kagouraki/windSensorYachta/Pictures/Yachta_Details/IMG_20210728_142634032_HDR_kl.jpg

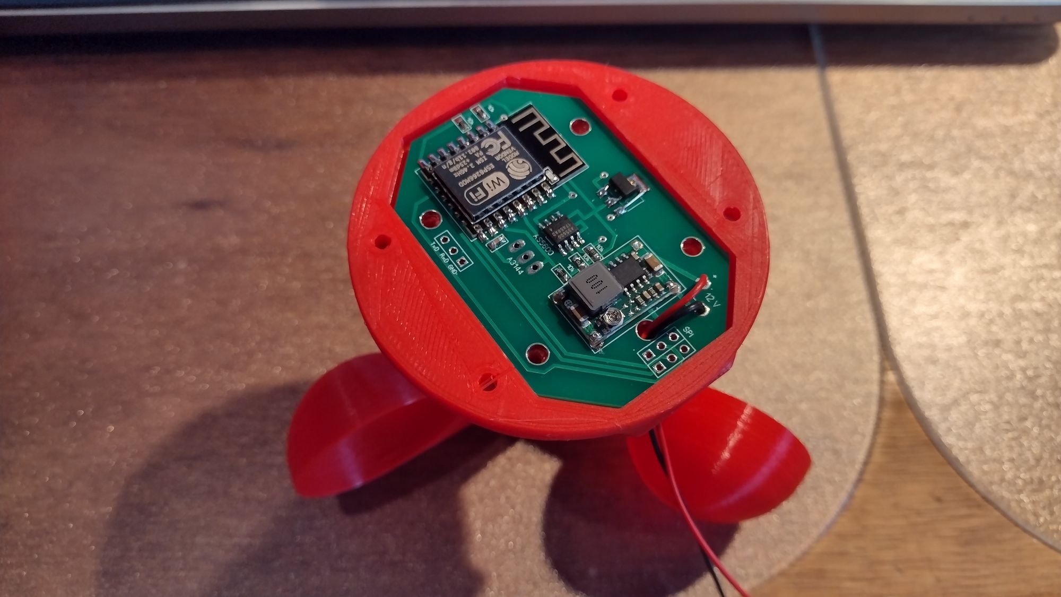
Pictures/Yachta_Details/IMG_20210728_142634032_HDR_kl.jpg
