kagouraki/windSensorYachta/Pictures/Yachta_Details/IMG_20210728_142640700_HDR_kl.jpg

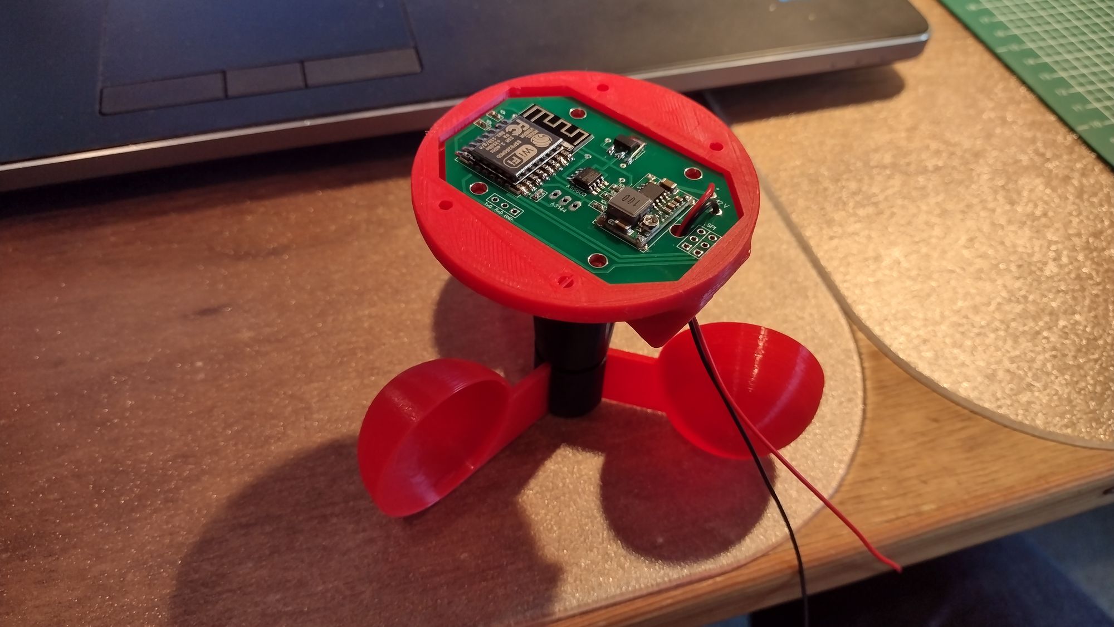
Pictures/Yachta_Details/IMG_20210728_142640700_HDR_kl.jpg
