kagouraki/windSensorYachta/Pictures/Yachta_Details/IMG_20210728_142648449_HDR_kl.jpg

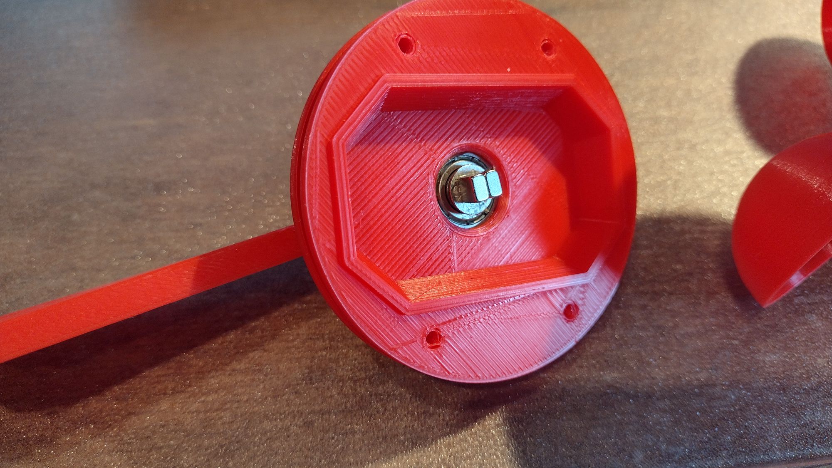
Pictures/Yachta_Details/IMG_20210728_142648449_HDR_kl.jpg
