kagouraki/windSensorYachta/Pictures/Yachta_Details/IMG_20210728_144132545_HDR_kl.jpg

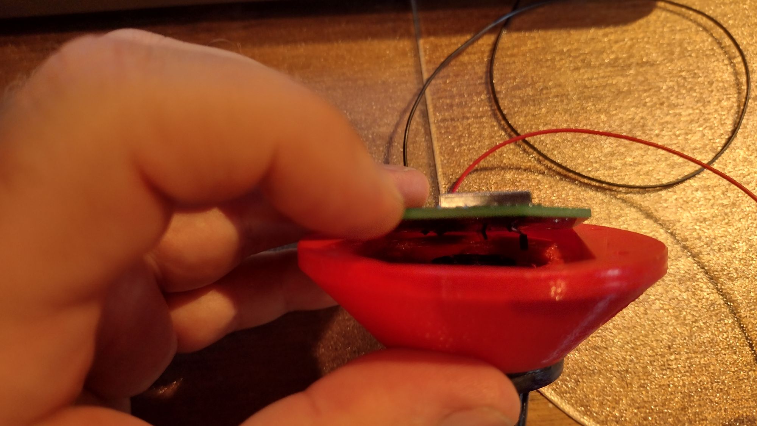
Pictures/Yachta_Details/IMG_20210728_144132545_HDR_kl.jpg
