kagouraki/windSensorYachta/Pictures/Yachta_Details/IMG_20210728_144154183_HDR_kl.jpg

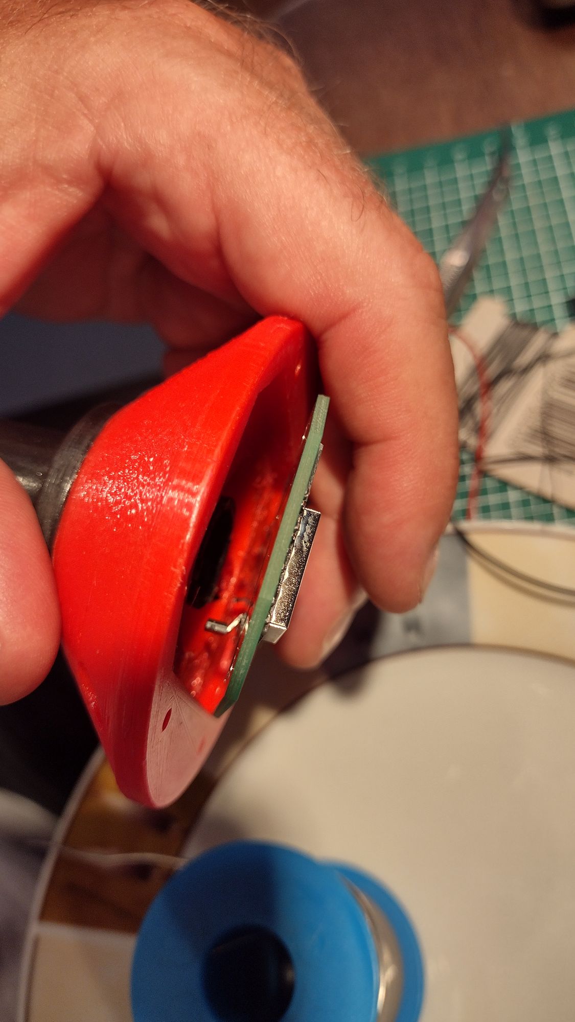
Pictures/Yachta_Details/IMG_20210728_144154183_HDR_kl.jpg
