kagouraki/windSensorYachta/Pictures/Yachta_Details/IMG_20210728_150717787_HDR_kl.jpg

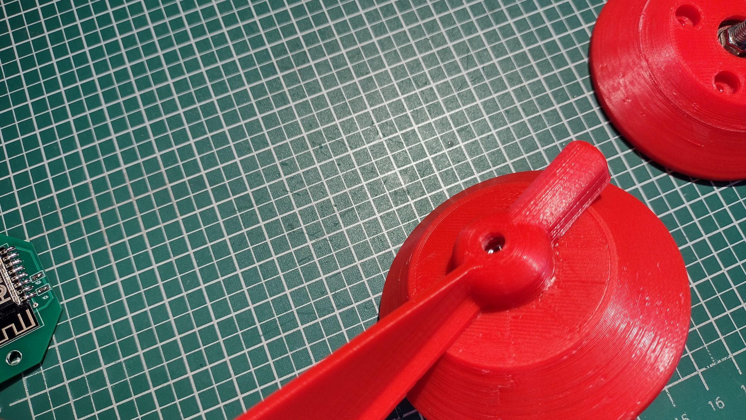
Pictures/Yachta_Details/IMG_20210728_150717787_HDR_kl.jpg
