kagouraki/windSensorYachta/Pictures/Yachta_Details/IMG_20210728_150723339_HDR_kl.jpg

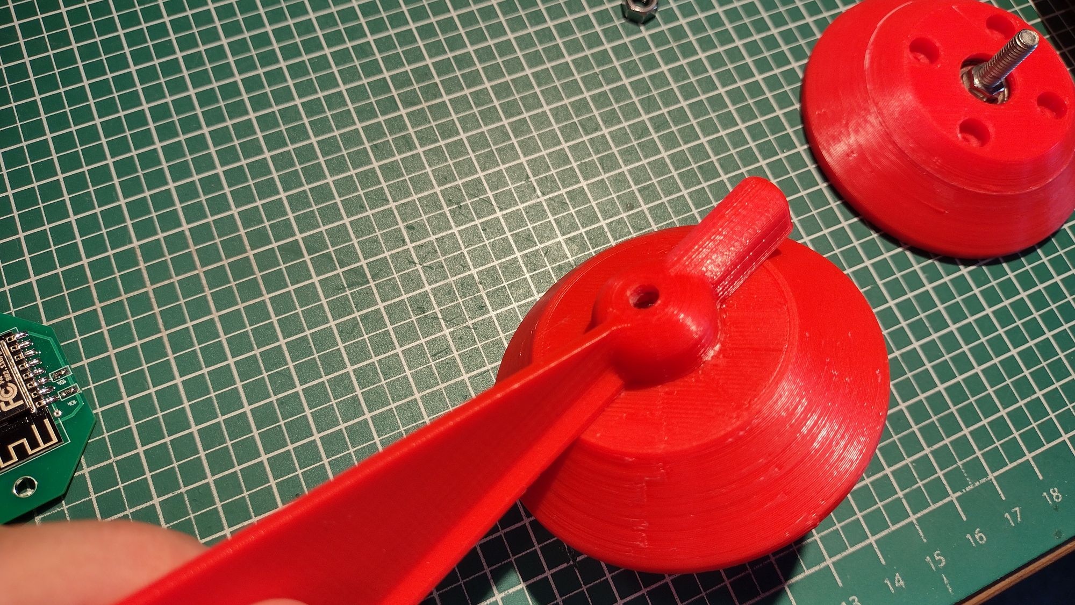
Pictures/Yachta_Details/IMG_20210728_150723339_HDR_kl.jpg
