kagouraki/windSensorYachta/Pictures/Yachta_Details/IMG_20210728_150742750_HDR_kl.jpg

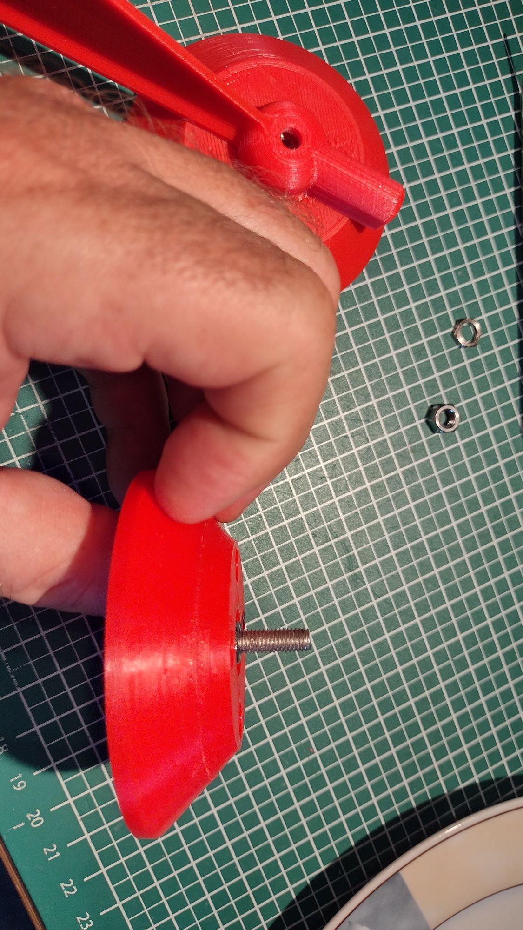
Pictures/Yachta_Details/IMG_20210728_150742750_HDR_kl.jpg
