kagouraki/windSensorYachta/Pictures/Yachta_Details/IMG_20210728_152233898_HDR_kl.jpg

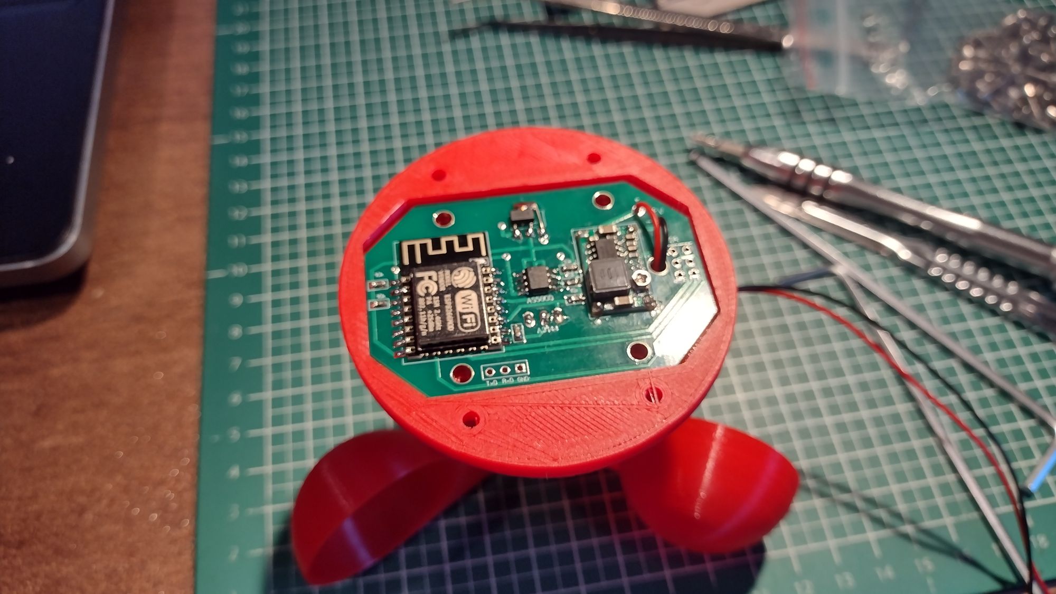
Pictures/Yachta_Details/IMG_20210728_152233898_HDR_kl.jpg
