kagouraki/windSensorYachta/Pictures/Yachta_Details/IMG_20210728_154134992_HDR_kl.jpg

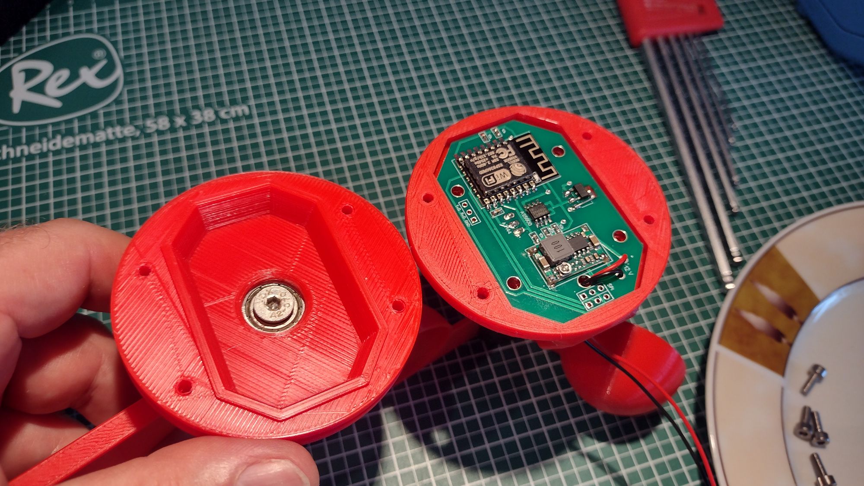
Pictures/Yachta_Details/IMG_20210728_154134992_HDR_kl.jpg
