kagouraki/windSensorYachta/Pictures/Yachta_Details/IMG_20210728_161656641_HDR_kl.jpg

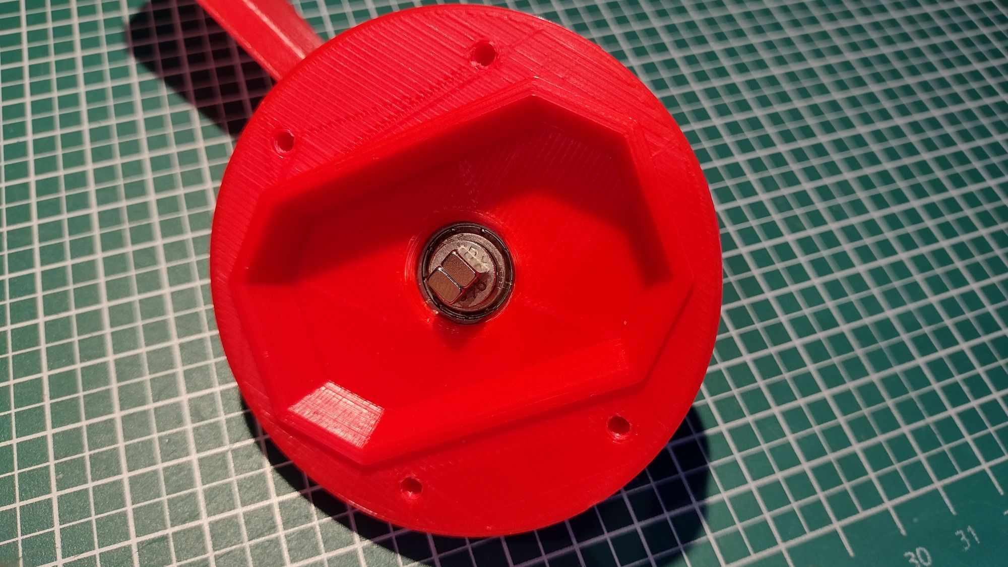
Pictures/Yachta_Details/IMG_20210728_161656641_HDR_kl.jpg
