kagouraki/windSensorYachta/Pictures/Yachta_Details/IMG_20210728_175009026_HDR_kl.jpg

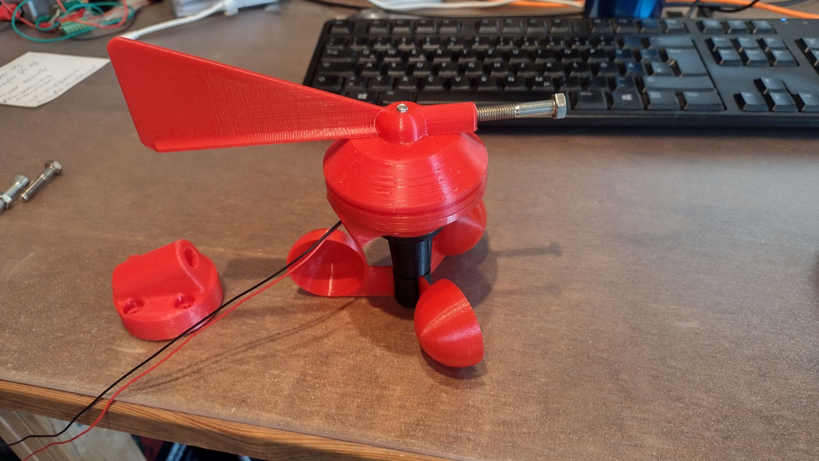
Pictures/Yachta_Details/IMG_20210728_175009026_HDR_kl.jpg
