kagouraki/windSensorYachta/Pictures/Yachta_Details/IMG_20210810_135746267_HDR_kl.jpg

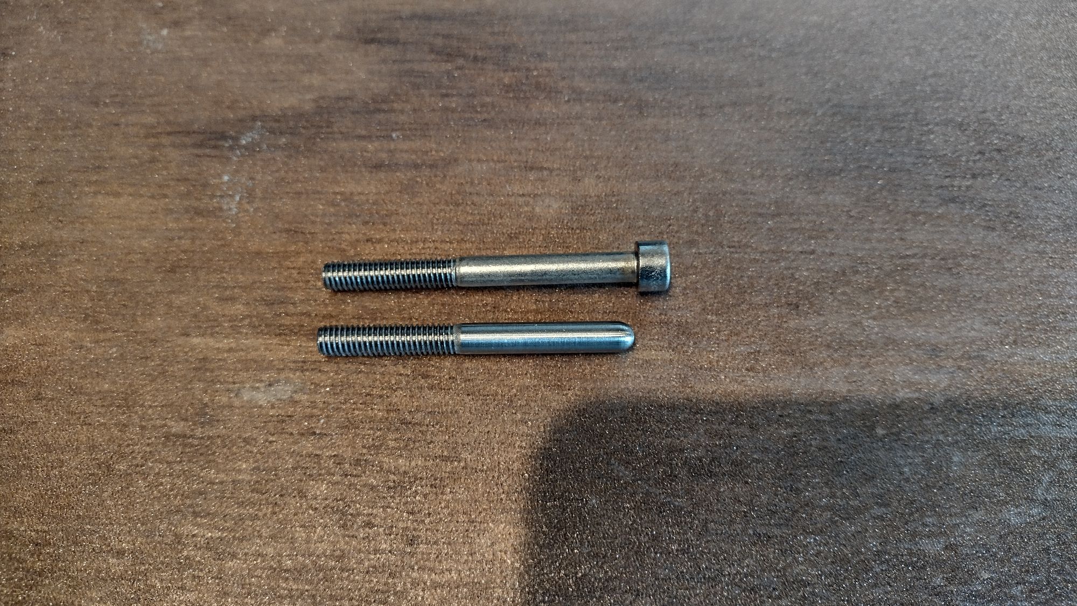
Pictures/Yachta_Details/IMG_20210810_135746267_HDR_kl.jpg
