kagouraki/windSensorYachta/Pictures/Yachta_Details/IMG_20210810_135933128_HDR_kl.jpg

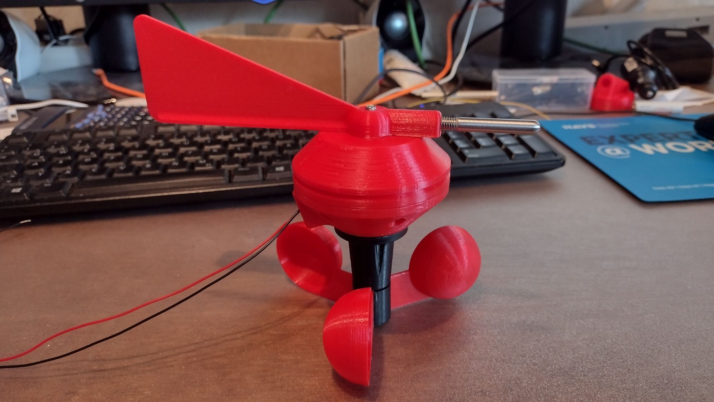
Pictures/Yachta_Details/IMG_20210810_135933128_HDR_kl.jpg
