kagouraki/windSensorYachta/Pictures/Yachta_Details/IMG_20210810_135939646_HDR_kl.jpg

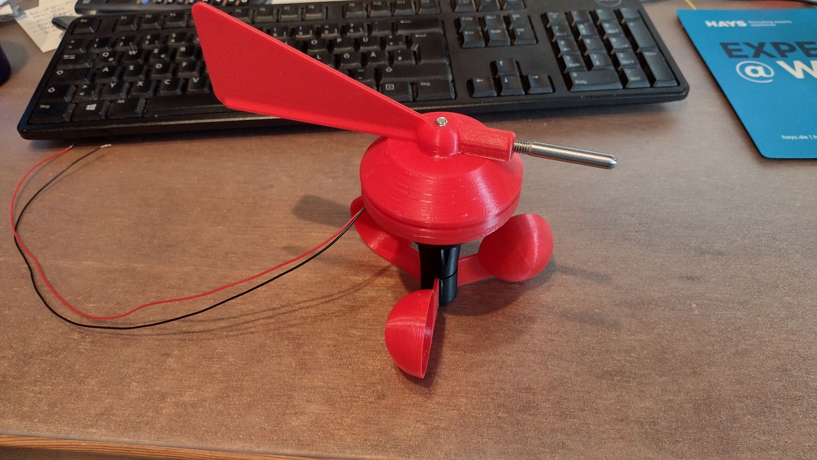
Pictures/Yachta_Details/IMG_20210810_135939646_HDR_kl.jpg
