kagouraki/windSensorYachta/Pictures/Yachta_Details/IMG_20210811_103145138_HDR_kl.jpg

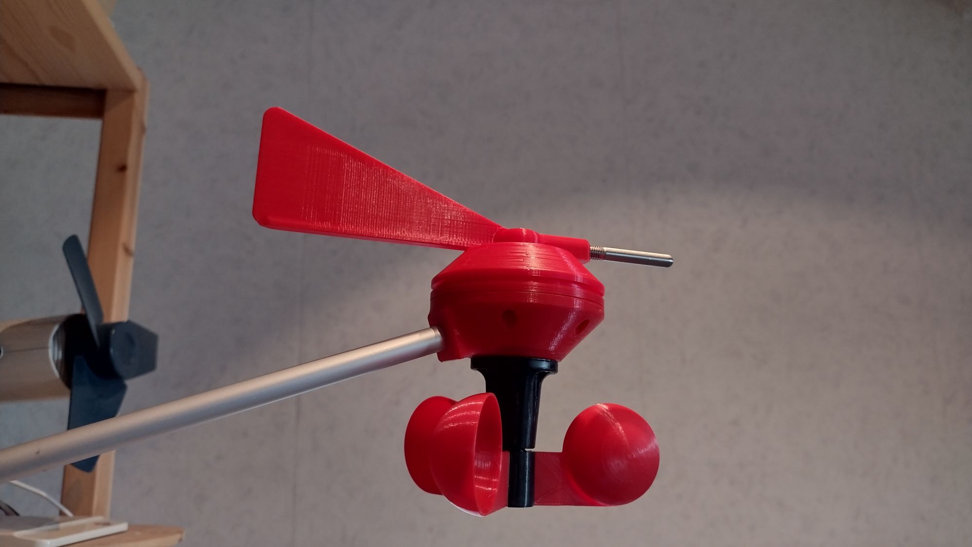
Pictures/Yachta_Details/IMG_20210811_103145138_HDR_kl.jpg
