kagouraki/windSensorYachta/Arduino Code/MyModifiedFW/steel_html.h

#pragma once
// JavaScript library steelseries_micro.js.gz as HEX coded char array
// The char array is stored in the PROGRAM memory

const char steelseries_micro_js_gz[] PROGMEM = {
0x1F, 0x8B, 0x08, 0x08, 0x7A, 0xDE, 0x09, 0x5F, 0x00, 0x03, 0x73, 0x74, 0x65, 0x65, 0x6C, 0x73, 
0x65, 0x72, 0x69, 0x65, 0x73, 0x35, 0x2E, 0x6A, 0x73, 0x00, 0xEC, 0x3D, 0x6B, 0x73, 0xDB, 0x38, 
0x92, 0xDF, 0xF7, 0x57, 0x30, 0x4A, 0x55, 0x4A, 0xB2, 0x61, 0x86, 0x0F, 0x51, 0x0F, 0x7B, 0xB8, 
0x53, 0xB2, 0x24, 0x27, 0xBA, 0x72, 0x6C, 0x9F, 0x28, 0x4F, 0x76, 0x6A, 0x2A, 0x75, 0x45, 0x8B, 
0xB4, 0xCC, 0x0D, 0x4D, 0x79, 0x49, 0x2A, 0x5E, 0xDF, 0x6C, 0xFE, 0xFB, 0x75, 0x83, 0x2F, 0x90, 
0x04, 0x28, 0xDA, 0xF1, 0xEE, 0xD6, 0xD5, 0x8E, 0x35, 0x52, 0x28, 0xA0, 0xD1, 0xE8, 0x17, 0xBA, 
0x1B, 0x4D, 0x50, 0xF3, 0xFE, 0xE0, 0xCD, 0x9F, 0xA4, 0x03, 0xE9, 0xC2, 0xBE, 0x77, 0xA5, 0xFC, 
0xEF, 0x58, 0x8A, 0x62, 0xD7, 0xF5, 0x23, 0x37, 0xF4, 0xDC, 0x48, 0x93, 0xFF, 0x1A, 0x21, 0xC8, 
0x64, 0x17, 0xDF, 0x6D, 0xC3, 0x28, 0x07, 0xF9, 0xE0, 0x86, 0xA1, 0x17, 0x4B, 0x1F, 0xC2, 0x5D, 
0xF0, 0x68, 0xFB, 0x0E, 0x91, 0x3E, 0xD9, 0xE1, 0x57, 0x69, 0x1A, 0x6E, 0xA3, 0xC8, 0x77, 0x9F, 
0x88, 0x74, 0xB1, 0x0D, 0x6F, 0xDC, 0x30, 0x96, 0x3E, 0xDB, 0x7E, 0xEC, 0x86, 0x88, 0xE1, 0xDC, 
0x8E, 0x62, 0xE9, 0x7E, 0xEB, 0x78, 0xB7, 0x9E, 0xEB, 0x00, 0x06, 0x75, 0x20, 0xAB, 0xAA, 0xAC, 
0x29, 0xEA, 0x08, 0x7B, 0x97, 0xEE, 0x37, 0x2F, 0xF2, 0xB6, 0x41, 0x86, 0x5F, 0x91, 0xD5, 0xBE, 
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
0x2C, 0x18, 0xD9, 0xA1, 0x1D, 0x93, 0x8B, 0x5F, 0xA5, 0xF9, 0x5F, 0xAE, 0x96, 0x73, 0xCB, 0x92, 
0x2E, 0x97, 0xD2, 0xE2, 0xD3, 0xD5, 0xF9, 0x02, 0x90, 0x01, 0xF6, 0xE5, 0xE4, 0x62, 0xB5, 0x98, 
0x5B, 0x44, 0x5A, 0x5C, 0x4C, 0xCF, 0xAF, 0x67, 0x8B, 0x8B, 0x0F, 0x24, 0x21, 0x01, 0xB0, 0x48, 
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
};
